gerisjd-netizen/mimiv-mini-update-version-/mimic_mini/IMG_20260921_205230.jpg

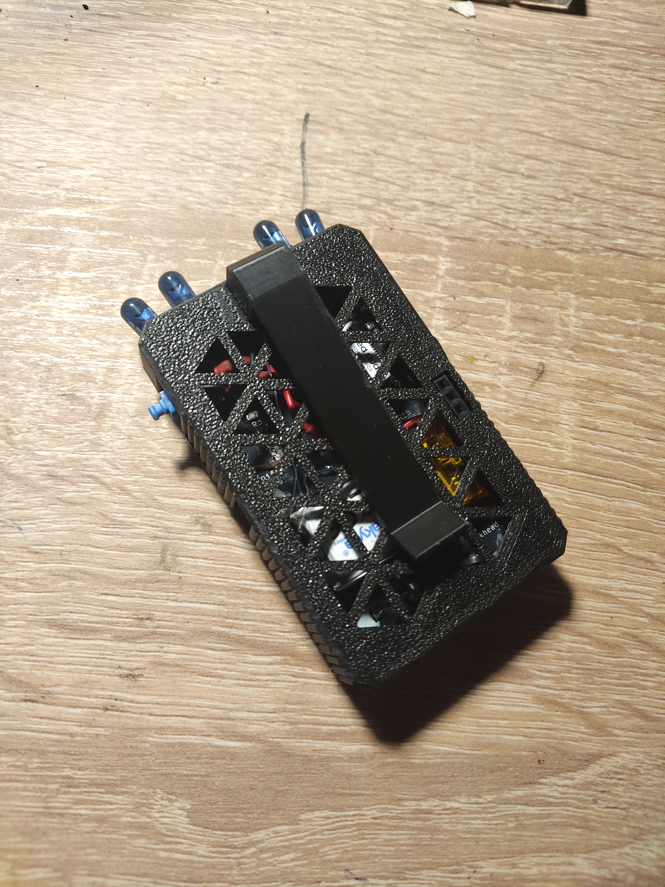
mimic_mini/IMG_20260921_205230.jpg
